adamm/rainbow-music-pegasus/firmware/main/config.c

#include <driver/gpio.h>
#include <esp_log.h>

#include "config.h"

const static char *TAG = "config";

uint8_t _config_total_leds = 0;
config_pattern_t _config_pattern = CONFIG_LEDS_PATTERN;
uint16_t _config_total_samples = 0;
uint32_t _config_sample_freq_hz = 0;

void config_init() {
    // Set the total number of leds configured by looking at the jumpers JP5, JP6, JP7. 
    // If they are closed they'll force the GPIO low.
    gpio_config_t io_conf = {
        .intr_type    = GPIO_INTR_DISABLE,
        .mode         = GPIO_MODE_INPUT,
        .pin_bit_mask = ((1ULL<<CONFIG_GPIO_TOTAL_LEDS_ADD_2) |
                         (1ULL<<CONFIG_GPIO_TOTAL_LEDS_ADD_4) |
                         (1ULL<<CONFIG_GPIO_TOTAL_LEDS_ADD_8)),
        .pull_up_en   = GPIO_PULLUP_ENABLE,
        .pull_down_en = GPIO_PULLDOWN_DISABLE,
    };
    gpio_config(&io_conf);

    _config_total_leds = CONFIG_MIN_LEDS;

    ESP_LOGI(TAG, "Minimum is %d", CONFIG_MIN_LEDS);
    if (gpio_get_level(CONFIG_GPIO_TOTAL_LEDS_ADD_2) == 0) {
        ESP_LOGI(TAG, "CONFIG_GPIO_TOTAL_LEDS_ADD_2 pin %d (JP7) is low/active", CONFIG_GPIO_TOTAL_LEDS_ADD_2);
        _config_total_leds += 2;
    }
    if (gpio_get_level(CONFIG_GPIO_TOTAL_LEDS_ADD_4) == 0) {
        ESP_LOGI(TAG, "CONFIG_GPIO_TOTAL_LEDS_ADD_4 pin %d (JP6) is low/active", CONFIG_GPIO_TOTAL_LEDS_ADD_4);
        _config_total_leds += 4;
    }
    if (gpio_get_level(CONFIG_GPIO_TOTAL_LEDS_ADD_8) == 0) {
        ESP_LOGI(TAG, "CONFIG_GPIO_TOTAL_LEDS_ADD_8 pin %d (JP5) is low/active", CONFIG_GPIO_TOTAL_LEDS_ADD_8);
        _config_total_leds += 8;
    }

    if (_config_total_leds > CONFIG_MAX_LEDS)
        _config_total_leds = CONFIG_MAX_LEDS;

    if (_config_total_leds <= 10)
        _config_total_samples = 64;
    else if (_config_total_leds <= 16)
        _config_total_samples = 128;
    else
        _config_total_samples = 256;

    // Patterns B and C show twice as many bins as A, so they take frames twice
    // as large to show the same range at the same sample rate.
    if (_config_pattern != CONFIG_PATTERN_A)
        _config_total_samples *= 2;

    // Each bin is the sample rate divided by the FFT size wide.  Pick the
    // sample rate that makes the shown bins end at the top frequency, so every
    // board shows the same range.
    uint32_t displayed_bins = config_displayed_bins();
    _config_sample_freq_hz = ((uint32_t)_config_total_samples * CONFIG_LEDS_TOP_FREQ_HZ + displayed_bins / 2) / displayed_bins;

    ESP_LOGI(TAG, "Total LEDs configured is %d", _config_total_leds);
    ESP_LOGI(TAG, "Showing %d bins in pattern %c", config_displayed_bins(), 'A' + _config_pattern);
    ESP_LOGI(TAG, "Total samples configured is %d", _config_total_samples);
    ESP_LOGI(TAG, "Sampling at %d Hz to show 0 to %d Hz", (int)_config_sample_freq_hz, CONFIG_LEDS_TOP_FREQ_HZ);
}


// How many of the lowest FFT bins the LEDs show: three per pair of LEDs in
// pattern A, and one per colour channel in the others.
uint16_t config_displayed_bins(void) {
    if (_config_pattern == CONFIG_PATTERN_A)
        return _config_total_leds * 3 / 2;
    return _config_total_leds * 3;
}
