adamm/rainbow-music-pegasus/firmware/test/fakes/soc/soc_caps.h

// The ESP32-C3's values.
#pragma once

#define SOC_ADC_DIGI_MAX_BITWIDTH       (12)
#define SOC_ADC_DIGI_RESULT_BYTES       (4)
#define SOC_ADC_SAMPLE_FREQ_THRES_HIGH  83333
#define SOC_ADC_SAMPLE_FREQ_THRES_LOW   611
#define SOC_GPIO_PIN_COUNT              22
